ctag-fh-kiel/ctag-straempler/components/audio/audio_luts.c

#include "audio_luts.h"


const float poti_vals[] = {
    20,2.026802e+01,2.053963e+01,2.081488e+01,2.109381e+01,2.137649e+01,2.166295e+01,2.195326e+01,
    2.224745e+01,2.254558e+01,2.284771e+01,2.315389e+01,2.346418e+01,2.377862e+01,2.409727e+01,
    2.442019e+01,2.474745e+01,2.507908e+01,2.541517e+01,2.575575e+01,2.610090e+01,2.645068e+01,
    2.680514e+01,2.716435e+01,2.752838e+01,2.789728e+01,2.827113e+01,2.864999e+01,2.903392e+01,
    2.942300e+01,2.981730e+01,3.021687e+01,3.062181e+01,3.103217e+01,3.144802e+01,3.186945e+01,
    3.229653e+01,3.272933e+01,3.316794e+01,3.361242e+01,3.406285e+01,3.451932e+01,3.498191e+01,
    3.545070e+01,3.592577e+01,3.640721e+01,3.689510e+01,3.738952e+01,3.789058e+01,3.839834e+01,
    3.891291e+01,3.943438e+01,3.996284e+01,4.049837e+01,4.104109e+01,4.159107e+01,4.214843e+01,
    4.271326e+01,4.328565e+01,4.386572e+01,4.445356e+01,4.504927e+01,4.565297e+01,4.626476e+01,
    4.688475e+01,4.751305e+01,4.814976e+01,4.879501e+01,4.944891e+01,5.011157e+01,5.078311e+01,
    5.146364e+01,5.215330e+01,5.285220e+01,5.356047e+01,5.427823e+01,5.500560e+01,5.574272e+01,
    5.648973e+01,5.724674e+01,5.801389e+01,5.879133e+01,5.957919e+01,6.037760e+01,6.118671e+01,
    6.200667e+01,6.283761e+01,6.367969e+01,6.453305e+01,6.539785e+01,6.627424e+01,6.716237e+01,
    6.806241e+01,6.897450e+01,6.989882e+01,7.083553e+01,7.178479e+01,7.274677e+01,7.372164e+01,
    7.470957e+01,7.571074e+01,7.672534e+01,7.775352e+01,7.879549e+01,7.985142e+01,8.092149e+01,
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
3172, 3254, 3338, 3424, 3513, 3604, 3697, 3792, 3890, 3991, 4094, 
4200, 4308, 4420, 4534, 4651, 4771, 4894, 5021, 5151, 5284, 5420, 
5560, 5704, 5852, 6003, 6158, 6317, 6480, 6648, 6820, 6996, 7177, 
7362, 7552, 7748, 7948, 8153, 8364, 8580, 8802, 9029, 9263, 9502, 
9748, 10000};
