ctag-fh-kiel/ctag-straempler/components/audio/include/audio_luts.h

#include "freertos/FreeRTOS.h"
extern const float poti_vals[512];
extern const float negative_freq_lut[512];
extern const float env_lut_float[512];
extern const float pitch_lut_24[25];
extern const float pitch_lut_1024[1281];
extern const float dist_q_lut[256];
extern const uint16_t msLut[256];
